hmatuschek/cwtrx/doc/fig/FrontPanel.png

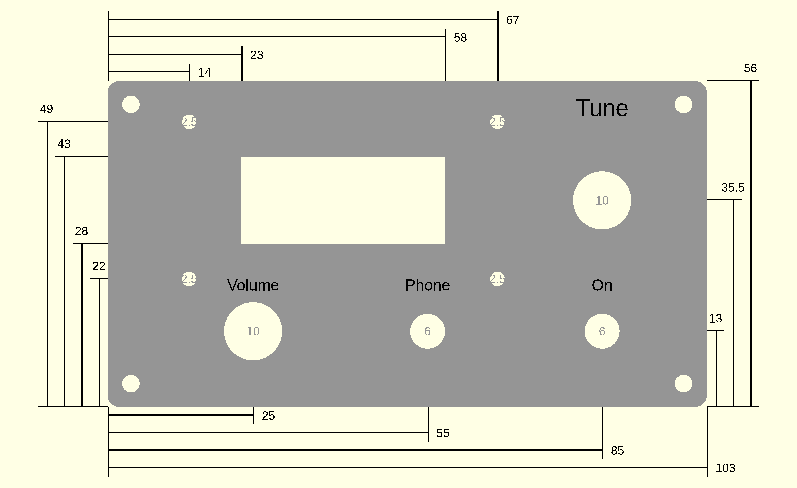
doc/fig/FrontPanel.png
