hmatuschek/cwtrx/doc/fig/RX_T1_IMG.jpg

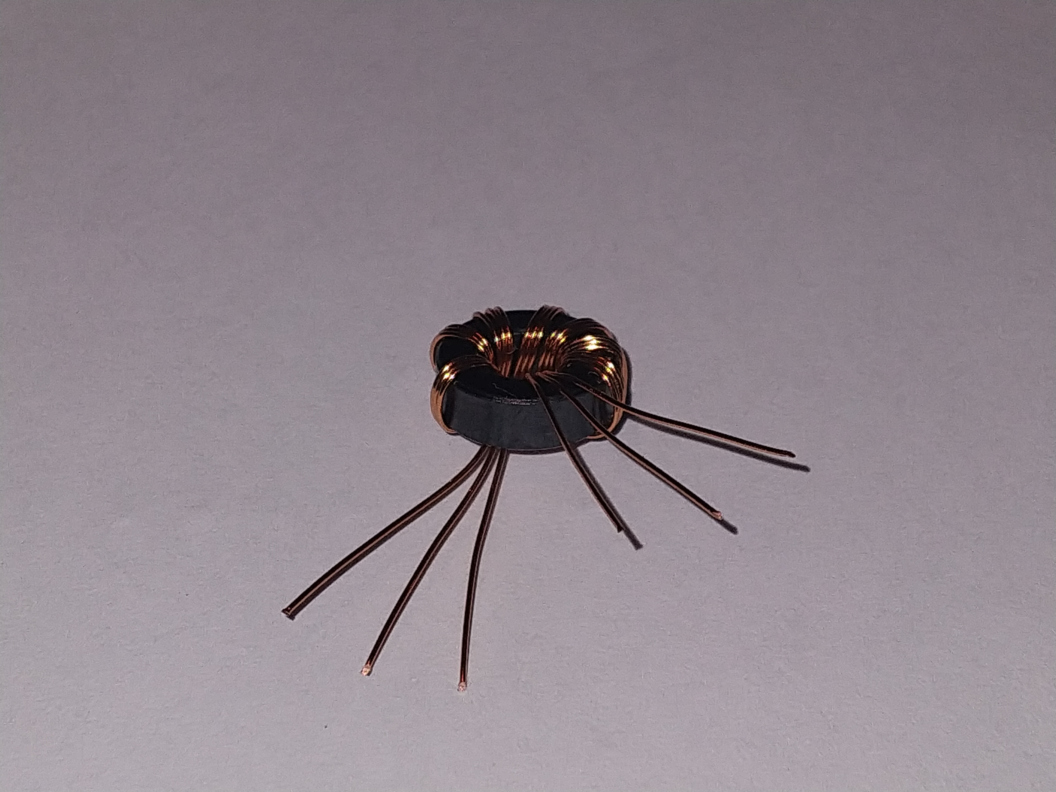
doc/fig/RX_T1_IMG.jpg
