hmatuschek/cwtrx/firmware/lcd.c

#include "lcd.h"
#include "trx.h"

#define LCD_BOOTUP_MS           45
#define LCD_ENABLE_US           20
#define LCD_WRITEDATA_US        46
#define LCD_COMMAND_US          50

#define LCD_SOFT_RESET_MS1      5
#define LCD_SOFT_RESET_MS2      1
#define LCD_SOFT_RESET_MS3      1
#define LCD_SET_4BITMODE_MS     5

#define LCD_CLEAR_DISPLAY_MS    2
#define LCD_CURSOR_HOME_MS      2

/* Zeilendefinitionen des verwendeten LCD
 * Die Einträge hier sollten für ein LCD mit einer Zeilenlänge von 16 Zeichen passen
 * Bei anderen Zeilenlängen müssen diese Einträge angepasst werden */

#define LCD_DDADR_LINE1         0x00
#define LCD_DDADR_LINE2         0x40
#define LCD_DDADR_LINE3         0x10
#define LCD_DDADR_LINE4         0x50

/* ********************************************************************************************* *
 * LCD Befehle und Argumente.
 * Zur Verwendung in lcd_command
 * ********************************************************************************************* */
// Clear Display -------------- 0b00000001
#define LCD_CLEAR_DISPLAY       0x01
// Cursor Home ---------------- 0b0000001x
#define LCD_CURSOR_HOME         0x02
// Set Entry Mode ------------- 0b000001xx
#define LCD_SET_ENTRY           0x04
#define LCD_ENTRY_DECREASE      0x00
#define LCD_ENTRY_INCREASE      0x02
#define LCD_ENTRY_NOSHIFT       0x00
#define LCD_ENTRY_SHIFT         0x01
// Set Display ---------------- 0b00001xxx
#define LCD_SET_DISPLAY         0x08
#define LCD_DISPLAY_OFF         0x00
#define LCD_DISPLAY_ON          0x04
#define LCD_CURSOR_OFF          0x00
#define LCD_CURSOR_ON           0x02
#define LCD_BLINKING_OFF        0x00
#define LCD_BLINKING_ON         0x01
// Set Shift ------------------ 0b0001xxxx
#define LCD_SET_SHIFT           0x10
#define LCD_CURSOR_MOVE         0x00
#define LCD_DISPLAY_SHIFT       0x08
#define LCD_SHIFT_LEFT          0x00
#define LCD_SHIFT_RIGHT         0x04
// Set Function --------------- 0b001xxxxx
#define LCD_SET_FUNCTION        0x20
#define LCD_FUNCTION_4BIT       0x00
#define LCD_FUNCTION_8BIT       0x10
#define LCD_FUNCTION_1LINE      0x00
#define LCD_FUNCTION_2LINE      0x08
#define LCD_FUNCTION_5X7        0x00
#define LCD_FUNCTION_5X10       0x04
// Set Reset --------------- 0b0011xxxx
#define LCD_SOFT_RESET          0x30
// Set CG RAM Address --------- 0b01xxxxxx  (Character Generator RAM)
#define LCD_SET_CGADR           0x40
#define LCD_GC_CHAR0            0
#define LCD_GC_CHAR1            1
#define LCD_GC_CHAR2            2
#define LCD_GC_CHAR3            3
#define LCD_GC_CHAR4            4
#define LCD_GC_CHAR5            5
#define LCD_GC_CHAR6            6
#define LCD_GC_CHAR7            7
// Set DD RAM Address --------- 0b1xxxxxxx  (Display Data RAM)
#define LCD_SET_DDADR           0x80


#include <util/delay.h>
#include <avr/pgmspace.h>

const uint8_t _lcd_sym_0[8] PROGMEM = {
  0b00000000,
  0b00000000,
  0b00000000,
  0b00000000,
  0b00000000,
  0b00000000,
  0b00011111,
  0b00000000
};

const uint8_t _lcd_sym_1[8] PROGMEM = {
  0b00000000,
  0b00000000,
  0b00000000,
  0b00000000,
  0b00000000,
  0b00011111,
  0b00011111,
  0b00000000
};

const uint8_t _lcd_sym_2[8] PROGMEM = {
  0b00000000,
  0b00000000,
  0b00000000,
  0b00011111,
  0b00011111,
  0b00011111,
  0b00011111,
  0b00000000
};

const uint8_t _lcd_sym_3[8] PROGMEM = {
  0b00000000,
  0b00011111,
  0b00011111,
  0b00011111,
  0b00011111,
  0b00011111,
  0b00011111,
  0b00000000
};

const uint8_t _lcd_sym_4[8] PROGMEM = {
  0b00011111,
  0b00011111,
  0b00011111,
  0b00011111,
  0b00011111,
  0b00011111,
  0b00011111,
  0b00000000
};

const uint8_t _lcd_sym_5[8] PROGMEM = {
  0b00011111,
  0b00000000,
  0b00011011,
  0b00011011,
  0b00011011,
  0b00011011,
  0b00011011,
  0b00000000
};

/*
 * Erzeugt einen Enable-Puls
 */
static void lcd_enable( void )
{
  LCDE_PORT |= (1<<LCD_EN);     // Enable auf 1 setzen
  _delay_us( LCD_ENABLE_US );   // kurze Pause
  LCDE_PORT &= ~(1<<LCD_EN);    // Enable auf 0 setzen
}

/*
 * Sendet eine 4-bit Ausgabeoperation an das LCD
 */
static void lcd_out( uint8_t data )
{
    data &= 0xF0;                       // obere 4 Bit maskieren

    LCDD_PORT &= ~(0xF0>>(4-LCD_DB));    // Maske löschen
    LCDD_PORT |= (data>>(4-LCD_DB));     // Bits setzen
    lcd_enable();
}

/*
 * Initialisierung: muss ganz am Anfang des Programms aufgerufen werden.
 */
void lcd_init( void )
{
    // verwendete Pins auf Ausgang schalten
    LCDR_DDR  |= (1 << LCD_RS);
    LCDR_PORT &= ~(1 << LCD_RS);
    LCDE_DDR  |= (1 << LCD_EN);
    LCDE_PORT &= ~(1 << LCD_EN);

    uint8_t pins = (0x0F << LCD_DB);             // 4 Datenleitungen
    LCDD_DDR  |= pins;

    // initial alle Ausgänge auf Null
    LCDD_PORT &= ~pins;

    // warten auf die Bereitschaft des LCD
    _delay_ms( LCD_BOOTUP_MS );

    // Soft-Reset muss 3mal hintereinander gesendet werden zur Initialisierung
    lcd_out( LCD_SOFT_RESET );
    _delay_ms( LCD_SOFT_RESET_MS1 );

    lcd_enable();
    _delay_ms( LCD_SOFT_RESET_MS2 );

    lcd_enable();
    _delay_ms( LCD_SOFT_RESET_MS3 );

    // 4-bit Modus aktivieren
    lcd_out( LCD_SET_FUNCTION |
             LCD_FUNCTION_4BIT );
    _delay_ms( LCD_SET_4BITMODE_MS );

    // 4-bit Modus / 2 Zeilen / 5x7
    lcd_command( LCD_SET_FUNCTION |
                 LCD_FUNCTION_4BIT |
                 LCD_FUNCTION_2LINE |
                 LCD_FUNCTION_5X7 );

    // Display aus / Cursor aus / Blinken aus
    lcd_command( LCD_SET_DISPLAY |
                 LCD_DISPLAY_OFF |
                 LCD_CURSOR_OFF |
                 LCD_BLINKING_OFF);

    // Clear display
    lcd_clear();

    // Cursor inkrement / kein Scrollen
    lcd_command( LCD_SET_ENTRY |
                 LCD_ENTRY_INCREASE |
                 LCD_ENTRY_NOSHIFT );

    // Display ein / Cursor aus / Blinken aus
    lcd_command( LCD_SET_DISPLAY |
                 LCD_DISPLAY_ON |
                 LCD_CURSOR_OFF |
                 LCD_BLINKING_OFF);

    // Load user defined chars
    uint8_t buffer[8];
    memcpy_P(buffer, _lcd_sym_0, 8);
    lcd_generatechar(LCD_GC_CHAR0, buffer);
    memcpy_P(buffer, _lcd_sym_1, 8);
    lcd_generatechar(LCD_GC_CHAR1, buffer);
    memcpy_P(buffer, _lcd_sym_2, 8);
    lcd_generatechar(LCD_GC_CHAR2, buffer);
    memcpy_P(buffer, _lcd_sym_3, 8);
    lcd_generatechar(LCD_GC_CHAR3, buffer);
    memcpy_P(buffer, _lcd_sym_4, 8);
    lcd_generatechar(LCD_GC_CHAR4, buffer);
    memcpy_P(buffer, _lcd_sym_5, 8);
    lcd_generatechar(LCD_GC_CHAR5, buffer);
}

/*
 * Sendet ein Datenbyte an das LCD
 */
void lcd_data( uint8_t data )
{
  // Time: 2*LCD_ENABLE_US + LCD_WRITEDATA_US
  // == 86us
    LCDR_PORT |= (1<<LCD_RS);    // RS auf 1 setzen

    lcd_out( data );            // zuerst die oberen,
    lcd_out( data<<4 );         // dann die unteren 4 Bit senden

    _delay_us( LCD_WRITEDATA_US );
}

/*
 * Sendet einen Befehl an das LCD
 */
void lcd_command( uint8_t data )
{
  // Time: 2*LCD_ENABLE_US + LCD_COMMAND_US
  //  == 82us
    LCDR_PORT &= ~(1<<LCD_RS);    // RS auf 0 setzen

    lcd_out( data );             // zuerst die oberen,
    lcd_out( data<<4 );           // dann die unteren 4 Bit senden

    _delay_us( LCD_COMMAND_US );
}

/*
 * Sendet den Befehl zur Löschung des Displays
 */
void lcd_clear( void )
{
    lcd_command( LCD_CLEAR_DISPLAY );
    _delay_ms( LCD_CLEAR_DISPLAY_MS );
}

/*
 * Sendet den Befehl: Cursor Home
 */
void lcd_home( void )
{
    lcd_command( LCD_CURSOR_HOME );
    _delay_ms( LCD_CURSOR_HOME_MS );
}

/*
 * Setzt den Cursor in Spalte x (0..15) Zeile y (1..4)
 */
void lcd_setcursor( uint8_t x, uint8_t y )
{
  uint8_t data;

  switch (y) {
    case 1:    // 1. Zeile
      data = LCD_SET_DDADR + LCD_DDADR_LINE1 + x;
      break;
    case 2:    // 2. Zeile
      data = LCD_SET_DDADR + LCD_DDADR_LINE2 + x;
      break;
    case 3:    // 3. Zeile
      data = LCD_SET_DDADR + LCD_DDADR_LINE3 + x;
      break;
    case 4:    // 4. Zeile
      data = LCD_SET_DDADR + LCD_DDADR_LINE4 + x;
      break;
    default:
      // für den Fall einer falschen Zeile
      return;
  }

  lcd_command( data );
}

void lcd_showcursor() {
  lcd_command( LCD_SET_DISPLAY |
               LCD_DISPLAY_ON |
               LCD_CURSOR_ON |
               LCD_BLINKING_OFF );
}

void lcd_blinkcursor() {
  lcd_command( LCD_SET_DISPLAY |
               LCD_DISPLAY_ON |
               LCD_CURSOR_ON |
               LCD_BLINKING_ON );
}

void lcd_hidecursor() {
  lcd_command( LCD_SET_DISPLAY |
               LCD_DISPLAY_ON |
               LCD_CURSOR_OFF |
               LCD_BLINKING_OFF);
}

/*
 * Schreibt einen String auf das LCD
 */
void lcd_string( const char *data )
{
  while( *data != '\0' )
    lcd_data( *data++ );
}

/*
 * Schreibt die Frequenz auf das Display (Laenge 8)
 */
void lcd_freq(uint32_t freq) {
  uint8_t leading=0, num=0;

  num = (freq / 10000000UL);
  freq = (freq % 10000000UL);
  if (num || leading) {
    lcd_data('0'+num); leading = 1;
  } else {
    lcd_data(' ');
  }
  num = (freq / 1000000UL);
  freq = (freq % 1000000UL);
  lcd_data('0'+num); leading = 1;

  num = (freq / 100000UL);
  freq = (freq % 100000UL);
  lcd_data('0'+num); leading = 1;
  num = (freq / 10000UL);
  freq = (freq % 10000UL);
  lcd_data('0'+num); leading = 1;
  num = (freq / 1000UL);
  freq = (freq % 1000UL);
  lcd_data('0'+num); leading = 1;
  lcd_data('.');

  num = (freq / 100UL);
  freq = (freq % 100UL);
  lcd_data('0'+num); leading = 1;
  num = (freq / 10UL);
  freq = (freq % 10UL);
  lcd_data('0'+num); leading = 1;
}

/*
 * Schreibt eine Zahl mit fester Breite auf das Display (rechtsbündig)
 */
void
lcd_print_uint16(uint16_t value, uint8_t width) {
  uint8_t buffer[6];
  uint8_t digits = 0;
  if (0 == value) {
    buffer[0] = '0';
    digits++;
  } else while (value) {
    uint8_t digit = value % 10; value /= 10;
    buffer[digits] = '0'+digit; digits++;
  }
  if (width>digits) {
    for (uint8_t i=0; i<(width-digits); i++)
      lcd_data(' ');
  }
  for (int8_t i=(digits-1); i>=0; i--) {
    lcd_data(buffer[i]);
  }
}


void
lcd_print_pllcorr(int32_t value) {
  uint8_t sign = (value<0) ? '-' : ' ';
  value = (value<0) ? -value : value;
  uint8_t dec = value % 10; value /= 10;
  value = ('-' == sign) ? -value : value;
  lcd_print_int32(value, 2);
  lcd_data('.');
  lcd_data('0'+dec);
  lcd_string("ppm");
}

void
lcd_print_int32(int32_t value, uint8_t width) {
  uint8_t sign = (value<0) ? '-' : ' ';
  value = (value<0) ? -value : value;
  uint8_t buffer[12];
  int8_t digits = 0;
  if (0 == value) {
    buffer[0] = '0'; digits++;
  } else while (value) {
    uint8_t digit = value%10; value /= 10;
    buffer[digits] = '0'+digit; digits++;
  }
  buffer[digits] = sign; digits++;
  if (digits < width) {
    for (uint8_t i=0; i<(width-digits); i++)
      lcd_data(' ');
  }
  for (int8_t i=(digits-1); i>=0; i--) {
    lcd_data(buffer[i]);
  }
}

/*
 * Schreibt ein Zeichen in den Character Generator RAM
 */
void lcd_generatechar(uint8_t addr, const uint8_t *data )
{
  // Startposition des Zeichens einstellen
  lcd_command( LCD_SET_CGADR | (addr<<3) );

  // Bitmuster übertragen
  for ( uint8_t i=0; i<8; i++ )
    lcd_data( data[i] );
  lcd_command(LCD_SET_DDADR); //DRAM auf 0 setzen
}
