hmatuschek/cwtrx/firmware/si5351.h

/*
 * si5351.h - Si5351 library for avr-gcc
 *
 * Copyright (C) 2014 Jason Milldrum <milldrum@gmail.com>
 *
 * Many defines derived from clk-si5351.h in the Linux kernel.
 * Sebastian Hesselbarth <sebastian.hesselbarth@gmail.com>
 * Rabeeh Khoury <rabeeh@solid-run.com>
 *
 * do_div() macro derived from /include/asm-generic/div64.h in
 * the Linux kernel.
 * Copyright (C) 2003 Bernardo Innocenti <bernie@develer.com>
 *
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
 * You should have received a copy of the GNU General Public License
 * along with this program.  If not, see <http://www.gnu.org/licenses/>.
 */

#include <avr/eeprom.h>

#ifndef SI5351_H_
#define SI5351_H_

/* Define definitions */

#define SI5351_BUS_BASE_ADDR				0xC0
#define SI5351_XTAL_FREQ					25000000
#define SI5351_PLL_FIXED					900000000

#define SI5351_PLL_VCO_MIN					600000000
#define SI5351_PLL_VCO_MAX					900000000
#define SI5351_MULTISYNTH_MIN_FREQ			1000000
#define SI5351_MULTISYNTH_DIVBY4_FREQ		150000000
#define SI5351_MULTISYNTH_MAX_FREQ			160000000
#define SI5351_MULTISYNTH67_MAX_FREQ		SI5351_MULTISYNTH_DIVBY4_FREQ
#define SI5351_CLKOUT_MIN_FREQ				8000
#define SI5351_CLKOUT_MAX_FREQ				SI5351_MULTISYNTH_MAX_FREQ
#define SI5351_CLKOUT67_MAX_FREQ			SI5351_MULTISYNTH67_MAX_FREQ

#define SI5351_PLL_A_MIN					15
#define SI5351_PLL_A_MAX					90
#define SI5351_PLL_B_MAX					(SI5351_PLL_C_MAX-1)
#define SI5351_PLL_C_MAX					1048575
#define SI5351_MULTISYNTH_A_MIN				6
#define SI5351_MULTISYNTH_A_MAX				1800
#define SI5351_MULTISYNTH67_A_MAX			254
#define SI5351_MULTISYNTH_B_MAX				(SI5351_MULTISYNTH_C_MAX-1)
#define SI5351_MULTISYNTH_C_MAX				1048575
#define SI5351_MULTISYNTH_P1_MAX			((1<<18)-1)
#define SI5351_MULTISYNTH_P2_MAX			((1<<20)-1)
#define SI5351_MULTISYNTH_P3_MAX			((1<<20)-1)

#define SI5351_DEVICE_STATUS				0
#define SI5351_INTERRUPT_STATUS				1
#define SI5351_INTERRUPT_MASK				2
#define  SI5351_STATUS_SYS_INIT				(1<<7)
#define  SI5351_STATUS_LOL_B				(1<<6)
#define  SI5351_STATUS_LOL_A				(1<<5)
#define  SI5351_STATUS_LOS					(1<<4)
#define SI5351_OUTPUT_ENABLE_CTRL			3
#define SI5351_OEB_PIN_ENABLE_CTRL			9
#define SI5351_PLL_INPUT_SOURCE				15
#define  SI5351_CLKIN_DIV_MASK				(3<<6)
#define  SI5351_CLKIN_DIV_1					(0<<6)
#define  SI5351_CLKIN_DIV_2					(1<<6)
#define  SI5351_CLKIN_DIV_4					(2<<6)
#define  SI5351_CLKIN_DIV_8					(3<<6)
#define  SI5351_PLLB_SOURCE					(1<<3)
#define  SI5351_PLLA_SOURCE					(1<<2)

#define SI5351_CLK0_CTRL					16
#define SI5351_CLK1_CTRL					17
#define SI5351_CLK2_CTRL					18
#define SI5351_CLK3_CTRL					19
#define SI5351_CLK4_CTRL					20
#define SI5351_CLK5_CTRL					21
#define SI5351_CLK6_CTRL					22
#define SI5351_CLK7_CTRL					23
#define  SI5351_CLK_POWERDOWN				(1<<7)
#define  SI5351_CLK_INTEGER_MODE			(1<<6)
#define  SI5351_CLK_PLL_SELECT				(1<<5)
#define  SI5351_CLK_INVERT					(1<<4)
#define  SI5351_CLK_INPUT_MASK				(3<<2)
#define  SI5351_CLK_INPUT_XTAL				(0<<2)
#define  SI5351_CLK_INPUT_CLKIN				(1<<2)
#define  SI5351_CLK_INPUT_MULTISYNTH_0_4	(2<<2)
#define  SI5351_CLK_INPUT_MULTISYNTH_N		(3<<2)
#define  SI5351_CLK_DRIVE_STRENGTH_MASK		(3<<0)
#define  SI5351_CLK_DRIVE_STRENGTH_2MA		(0<<0)
#define  SI5351_CLK_DRIVE_STRENGTH_4MA		(1<<0)
#define  SI5351_CLK_DRIVE_STRENGTH_6MA		(2<<0)
#define  SI5351_CLK_DRIVE_STRENGTH_8MA		(3<<0)

#define SI5351_CLK3_0_DISABLE_STATE			24
#define SI5351_CLK7_4_DISABLE_STATE			25
#define  SI5351_CLK_DISABLE_STATE_MASK		3
#define  SI5351_CLK_DISABLE_STATE_LOW		0
#define  SI5351_CLK_DISABLE_STATE_HIGH		1
#define  SI5351_CLK_DISABLE_STATE_FLOAT		2
#define  SI5351_CLK_DISABLE_STATE_NEVER		3

#define SI5351_PARAMETERS_LENGTH			8
#define SI5351_PLLA_PARAMETERS				26
#define SI5351_PLLB_PARAMETERS				34
#define SI5351_CLK0_PARAMETERS				42
#define SI5351_CLK1_PARAMETERS				50
#define SI5351_CLK2_PARAMETERS				58
#define SI5351_CLK3_PARAMETERS				66
#define SI5351_CLK4_PARAMETERS				74
#define SI5351_CLK5_PARAMETERS				82
#define SI5351_CLK6_PARAMETERS				90
#define SI5351_CLK7_PARAMETERS				91
#define SI5351_CLK6_7_OUTPUT_DIVIDER		92
#define  SI5351_OUTPUT_CLK_DIV_MASK			(7 << 4)
#define  SI5351_OUTPUT_CLK6_DIV_MASK		(7 << 0)
#define  SI5351_OUTPUT_CLK_DIV_SHIFT		4
#define  SI5351_OUTPUT_CLK_DIV6_SHIFT		0
#define  SI5351_OUTPUT_CLK_DIV_1			0
#define  SI5351_OUTPUT_CLK_DIV_2			1
#define  SI5351_OUTPUT_CLK_DIV_4			2
#define  SI5351_OUTPUT_CLK_DIV_8			3
#define  SI5351_OUTPUT_CLK_DIV_16			4
#define  SI5351_OUTPUT_CLK_DIV_32			5
#define  SI5351_OUTPUT_CLK_DIV_64			6
#define  SI5351_OUTPUT_CLK_DIV_128			7
#define  SI5351_OUTPUT_CLK_DIVBY4			(3<<2)

#define SI5351_SSC_PARAM0					149
#define SI5351_SSC_PARAM1					150
#define SI5351_SSC_PARAM2					151
#define SI5351_SSC_PARAM3					152
#define SI5351_SSC_PARAM4					153
#define SI5351_SSC_PARAM5					154
#define SI5351_SSC_PARAM6					155
#define SI5351_SSC_PARAM7					156
#define SI5351_SSC_PARAM8					157
#define SI5351_SSC_PARAM9					158
#define SI5351_SSC_PARAM10					159
#define SI5351_SSC_PARAM11					160
#define SI5351_SSC_PARAM12					161

#define SI5351_VXCO_PARAMETERS_LOW			162
#define SI5351_VXCO_PARAMETERS_MID			163
#define SI5351_VXCO_PARAMETERS_HIGH			164

#define SI5351_CLK0_PHASE_OFFSET			165
#define SI5351_CLK1_PHASE_OFFSET			166
#define SI5351_CLK2_PHASE_OFFSET			167
#define SI5351_CLK3_PHASE_OFFSET			168
#define SI5351_CLK4_PHASE_OFFSET			169
#define SI5351_CLK5_PHASE_OFFSET			170

#define SI5351_PLL_RESET					177
#define  SI5351_PLL_RESET_B				(1<<7)
#define  SI5351_PLL_RESET_A				(1<<5)

#define SI5351_CRYSTAL_LOAD				183
#define  SI5351_CRYSTAL_LOAD_MASK		(3<<6)
#define  SI5351_CRYSTAL_LOAD_6PF		(1<<6)
#define  SI5351_CRYSTAL_LOAD_8PF		(2<<6)
#define  SI5351_CRYSTAL_LOAD_10PF		(3<<6)

#define SI5351_FANOUT_ENABLE			187
#define  SI5351_CLKIN_ENABLE			(1<<7)
#define  SI5351_XTAL_ENABLE				(1<<6)
#define  SI5351_MULTISYNTH_ENABLE		(1<<4)

/* Macro definitions */

/*
 * Based on former asm-ppc/div64.h and asm-m68knommu/div64.h
 *
 * The semantics of do_div() are:
 *
 * uint32_t do_div(uint64_t *n, uint32_t base)
 * {
 *      uint32_t remainder = *n % base;
 *      *n = *n / base;
 *      return remainder;
 * }
 *
 * NOTE: macro parameter n is evaluated multiple times,
 *       beware of side effects!
 */

# define do_div(n,base) ({                                      \
        uint32_t __base = (base);                               \
        uint32_t __rem;                                         \
        __rem = ((uint64_t)(n)) % __base;                       \
        (n) = ((uint64_t)(n)) / __base;                         \
        __rem;                                                  \
 })

/* Enum definitions */

/*
 * enum si5351_variant - SiLabs Si5351 chip variant
 * @SI5351_VARIANT_A: Si5351A (8 output clocks, XTAL input)
 * @SI5351_VARIANT_A3: Si5351A MSOP10 (3 output clocks, XTAL input)
 * @SI5351_VARIANT_B: Si5351B (8 output clocks, XTAL/VXCO input)
 * @SI5351_VARIANT_C: Si5351C (8 output clocks, XTAL/CLKIN input)
 */
enum si5351_variant {
	SI5351_VARIANT_A = 1,
	SI5351_VARIANT_A3 = 2,
	SI5351_VARIANT_B = 3,
	SI5351_VARIANT_C = 4,
};

enum si5351_clock {SI5351_CLK0, SI5351_CLK1, SI5351_CLK2, SI5351_CLK3,
	SI5351_CLK4, SI5351_CLK5, SI5351_CLK6, SI5351_CLK7};

enum si5351_pll {SI5351_PLLA, SI5351_PLLB};

enum si5351_drive {SI5351_DRIVE_2MA, SI5351_DRIVE_4MA, SI5351_DRIVE_6MA, SI5351_DRIVE_8MA};

/* Struct definitions */

struct Si5351RegSet
{
	uint32_t p1;
	uint32_t p2;
	uint32_t p3;
};

struct Si5351Status
{
	uint8_t SYS_INIT;
	uint8_t LOL_B;
	uint8_t LOL_A;
	uint8_t LOS;
	uint8_t REVID;
};

struct Si5351IntStatus
{
	uint8_t SYS_INIT_STKY;
	uint8_t LOL_B_STKY;
	uint8_t LOL_A_STKY;
	uint8_t LOS_STKY;
};

/* Suggested public function prototypes */

uint8_t si5351_init(void);
void si5351_set_freq(uint32_t, uint32_t, enum si5351_clock);
void si5351_set_pll(uint32_t, enum si5351_pll);
void si5351_clock_enable(enum si5351_clock, uint8_t);
void si5351_drive_strength(enum si5351_clock, enum si5351_drive);
void si5351_update_status(void);
void si5351_set_correction(int32_t);
int32_t si5351_get_correction(void);

/* Suggested private function prototypes */

void rational_best_approximation(uint32_t, uint32_t, uint32_t, uint32_t, uint32_t*, uint32_t *);
uint32_t pll_calc(uint32_t, struct Si5351RegSet *, int32_t);
uint32_t multisynth_calc(uint32_t, struct Si5351RegSet *);
uint32_t multisynth_recalc(uint32_t, uint32_t,struct Si5351RegSet *);
uint8_t si5351_write_bulk(uint8_t, uint8_t, uint8_t *);
uint8_t si5351_write(uint8_t, uint8_t);
uint8_t si5351_read(uint8_t, uint8_t *);
void si5351_update_sys_status(struct Si5351Status *);
void si5351_update_int_status(struct Si5351IntStatus *);
void si5351_set_ms_source(enum si5351_clock, enum si5351_pll);

#endif /* SI5351_H_ */
